lordfarq/openflight/src/openflight/rolling_buffer/monitor.py

"""
Rolling Buffer Monitor - Alternative to LaunchMonitor for rolling buffer mode.

Provides the same interface as LaunchMonitor but uses rolling buffer capture
and post-processing for higher resolution speed data and spin detection.
"""

import logging
import statistics
import threading
import time
from datetime import datetime
from typing import Callable, List, Optional

from ..launch_monitor import ClubType, Shot, estimate_carry_distance
from ..ops243 import OPS243Radar, SpeedReading
from ..session_logger import get_session_logger
from .processor import RollingBufferProcessor
from .trigger import create_trigger
from .types import ProcessedCapture

logger = logging.getLogger("openflight.rolling_buffer.monitor")


def get_optimal_spin_for_ball_speed(ball_speed_mph: float, club: ClubType = ClubType.DRIVER) -> float:
    """
    Get optimal spin rate for a given ball speed.

    Based on TrackMan/PING research data:
    - Higher ball speeds require LESS spin for optimal carry
    - Lower ball speeds need MORE spin to maintain lift

    Reference data points (driver):
    - 120 mph ball speed → ~2900 rpm optimal
    - 140 mph ball speed → ~2700 rpm optimal
    - 160 mph ball speed → ~2550 rpm optimal (Tour average zone)
    - 180 mph ball speed → ~2050 rpm optimal

    Args:
        ball_speed_mph: Ball speed in mph
        club: Club type (affects optimal spin)

    Returns:
        Optimal spin rate in RPM
    """
    # Driver optimal spin (baseline) - interpolated from TrackMan/PING data
    # Table: (min_speed, base_rpm_at_upper_bound, rpm_per_mph_below_upper, upper_bound)
    _spin_table = [
        (180, 2050, 0, 999),
        (170, 2050, 25, 180),
        (160, 2300, 25, 170),
        (140, 2550, 7.5, 160),
        (120, 2700, 10, 140),
        (100, 2900, 10, 120),
    ]

    optimal = 3200  # Default for speeds below 100 mph
    for min_speed, base_rpm, rpm_per_mph, upper in _spin_table:
        if ball_speed_mph >= min_speed:
            optimal = base_rpm + (upper - ball_speed_mph) * rpm_per_mph
            break

    # Adjust for club type - irons need more spin
    club_spin_multipliers = {
        ClubType.DRIVER: 1.0,
        ClubType.WOOD_3: 1.15,
        ClubType.WOOD_5: 1.25,
        ClubType.WOOD_7: 1.32,
        ClubType.HYBRID_3: 1.45,
        ClubType.HYBRID_5: 1.55,
        ClubType.HYBRID_7: 1.65,
        ClubType.HYBRID_9: 1.75,
        ClubType.IRON_2: 1.5,
        ClubType.IRON_3: 1.6,
        ClubType.IRON_4: 1.8,
        ClubType.IRON_5: 2.0,
        ClubType.IRON_6: 2.2,
        ClubType.IRON_7: 2.5,
        ClubType.IRON_8: 2.8,
        ClubType.IRON_9: 3.2,
        ClubType.PW: 3.6,
        ClubType.GW: 4.1,
        ClubType.SW: 4.3,
        ClubType.LW: 4.6,
        ClubType.UNKNOWN: 1.0,
    }

    multiplier = club_spin_multipliers.get(club, 1.0)
    return optimal * multiplier


def estimate_carry_with_spin(
    ball_speed_mph: float,
    spin_rpm: float,
    club: ClubType = ClubType.DRIVER,
    club_speed_mph: Optional[float] = None,
) -> float:
    """
    Estimate carry distance using ball speed, spin rate, and optional club speed.

    Based on TrackMan/PING research data and physics:
    - Ball speed is primary factor (~85% of distance variance)
    - Spin rate affects trajectory via Magnus effect (lift)
    - Optimal spin varies inversely with ball speed
    - Smash factor validates contact quality

    Reference data points (driver, optimal conditions):
    - 120 mph ball speed → ~198 yards carry
    - 140 mph ball speed → ~231 yards carry
    - 160 mph ball speed → ~271 yards carry (Tour average: 167 mph → 275 yds)
    - 180 mph ball speed → ~310 yards carry

    Spin effects:
    - Too LOW: Ball "falls out of sky" - significant distance loss
    - Optimal: Maximum carry for given ball speed
    - Too HIGH: Ball "balloons" - moderate distance loss

    Args:
        ball_speed_mph: Ball speed in mph
        spin_rpm: Spin rate in RPM
        club: Club type for distance calculation
        club_speed_mph: Optional club head speed for smash factor validation

    Returns:
        Estimated carry distance in yards
    """
    # Get base carry from existing lookup table (TrackMan-derived)
    base_carry = estimate_carry_distance(ball_speed_mph, club)

    # Calculate optimal spin for this ball speed and club
    optimal_spin = get_optimal_spin_for_ball_speed(ball_speed_mph, club)

    # Calculate spin deviation
    spin_delta = spin_rpm - optimal_spin
    spin_delta_abs = abs(spin_delta)

    # Apply asymmetric spin adjustment
    # Low spin hurts MORE than high spin (ball falls out of sky vs balloons)
    if spin_delta < 0:
        # LOW SPIN: More severe penalty
        # Research shows ~1.2 yards lost per 100 rpm below optimal
        # Cap at 18% max penalty for extremely low spin
        penalty_per_100rpm = 0.012  # 1.2% per 100 rpm
        spin_factor = 1.0 - (spin_delta_abs / 100) * penalty_per_100rpm
        spin_factor = max(0.82, spin_factor)
    else:
        # HIGH SPIN: Less severe penalty (ball balloons but still carries)
        # Research shows ~0.8 yards lost per 100 rpm above optimal
        # Cap at 12% max penalty for extremely high spin
        penalty_per_100rpm = 0.008  # 0.8% per 100 rpm
        spin_factor = 1.0 - (spin_delta_abs / 100) * penalty_per_100rpm
        spin_factor = max(0.88, spin_factor)

    # Slight bonus for being very close to optimal (within 200 rpm)
    if spin_delta_abs < 200:
        spin_factor = min(1.02, spin_factor + 0.01)

    # Smash factor quality adjustment (if club speed available)
    smash_factor_adj = 1.0
    if club_speed_mph and club_speed_mph > 0:
        smash = ball_speed_mph / club_speed_mph

        # Optimal smash factors by club type
        optimal_smash = {
            ClubType.DRIVER: 1.48,
            ClubType.WOOD_3: 1.44,
            ClubType.WOOD_5: 1.42,
            ClubType.WOOD_7: 1.41,
            ClubType.HYBRID_3: 1.39,
            ClubType.HYBRID_5: 1.37,
            ClubType.HYBRID_7: 1.35,
            ClubType.HYBRID_9: 1.33,
            ClubType.IRON_2: 1.36,
            ClubType.IRON_3: 1.35,
            ClubType.IRON_4: 1.33,
            ClubType.IRON_5: 1.31,
            ClubType.IRON_6: 1.29,
            ClubType.IRON_7: 1.27,
            ClubType.IRON_8: 1.25,
            ClubType.IRON_9: 1.23,
            ClubType.PW: 1.21,
            ClubType.GW: 1.19,
            ClubType.SW: 1.18,
            ClubType.LW: 1.17,
            ClubType.UNKNOWN: 1.35,
        }

        target_smash = optimal_smash.get(club, 1.35)
        smash_delta = target_smash - smash

        if smash_delta > 0:
            # Below optimal smash = off-center hit = less efficient energy transfer
            # Penalize ~3% per 0.05 smash factor below optimal
            smash_factor_adj = max(0.94, 1.0 - (smash_delta / 0.05) * 0.03)
        elif smash_delta < -0.05:
            # Unusually high smash factor (>1.53 for driver) - might be measurement error
            # Or could indicate gear effect adding speed - slight penalty for uncertainty
            smash_factor_adj = 0.98

    # Final calculation
    adjusted_carry = base_carry * spin_factor * smash_factor_adj

    return adjusted_carry


class RollingBufferMonitor:
    """
    Golf Launch Monitor using rolling buffer mode.

    Alternative to LaunchMonitor that captures raw I/Q data for post-processing.
    Provides higher temporal resolution (~937 Hz vs ~56 Hz) and optional spin
    detection.

    Recommended configuration uses "speed" trigger (default):
    - Fast speed detection mode (~150-200Hz) watches for club swing
    - Automatically switches to rolling buffer when speed detected
    - Captures ball impact with high temporal resolution
    - Per OmniPreSense manufacturer recommendation

    Interface matches LaunchMonitor for compatibility with existing code.

    Example:
        monitor = RollingBufferMonitor()  # Uses speed trigger by default
        monitor.connect()
        monitor.start(shot_callback=on_shot)

        # Wait for shots...

        monitor.stop()
        monitor.disconnect()
    """

    def __init__(
        self,
        port: Optional[str] = None,
        trigger_type: str = "speed",
        sample_rate_ksps: int = 30,
        **trigger_kwargs,
    ):
        """
        Initialize rolling buffer monitor.

        Args:
            port: Serial port for radar. Auto-detect if None.
            trigger_type: Trigger strategy:
                - "speed" (default, recommended): Fast speed trigger per manufacturer
                - "polling": Continuous capture polling (slower, simpler)
                - "threshold": Speed threshold trigger
                - "manual": External trigger for testing
            **trigger_kwargs: Arguments for trigger strategy
        """
        self.radar = OPS243Radar(port=port)
        self.processor = RollingBufferProcessor(sample_rate=sample_rate_ksps * 1000)
        self.trigger_type = trigger_type
        self.sample_rate_ksps = sample_rate_ksps
        self.trigger = create_trigger(trigger_type, **trigger_kwargs)

        self._running = False
        self._capture_thread: Optional[threading.Thread] = None
        self._shot_callback: Optional[Callable[[Shot], None]] = None
        self._live_callback: Optional[Callable[[SpeedReading], None]] = None
        self._shots: List[Shot] = []
        self._current_club: ClubType = ClubType.DRIVER

    def connect(self) -> bool:
        """
        Connect to radar and configure based on trigger type.

        For "speed" trigger: Configuration is handled by the trigger strategy
        For other triggers: Configure for rolling buffer mode with appropriate
        pre_trigger_segments from the trigger.

        Returns:
            True if successful
        """
        self.radar.connect()

        # Speed trigger handles its own configuration (starts in speed mode)
        # Other triggers need rolling buffer mode configured upfront
        if self.trigger_type != "speed":
            # Get pre_trigger_segments from the trigger if available
            pre_trigger_segments = getattr(self.trigger, 'pre_trigger_segments', 12)
            self.radar.configure_for_rolling_buffer(
                pre_trigger_segments=pre_trigger_segments,
                sample_rate_ksps=self.sample_rate_ksps,
            )
            logger.info("Rolling buffer mode configured with S#%d, S=%d", pre_trigger_segments, self.sample_rate_ksps)
        else:
            logger.info("Using speed trigger - configuration deferred to trigger")

        return True

    def disconnect(self):
        """Disconnect from radar."""
        self.stop()
        self.radar.disable_rolling_buffer()
        self.radar.disconnect()

    def get_radar_info(self) -> dict:
        """Get radar module information."""
        return self.radar.get_info()

    def start(
        self,
        shot_callback: Optional[Callable[[Shot], None]] = None,
        live_callback: Optional[Callable[[SpeedReading], None]] = None,
        diagnostic_callback: Optional[Callable[[dict], None]] = None,
    ):
        """
        Start monitoring for shots.

        Args:
            shot_callback: Called when a complete shot is detected
            live_callback: Called for live readings (limited in rolling buffer mode)
            diagnostic_callback: Called with trigger diagnostic data for UI display
        """
        self._shot_callback = shot_callback
        self._live_callback = live_callback
        self._diagnostic_callback = diagnostic_callback
        self._running = True

        self._capture_thread = threading.Thread(
            target=self._capture_loop,
            daemon=True,
        )
        self._capture_thread.start()

        logger.info("Rolling buffer monitor started (trigger: %s)", self.trigger_type)

    def stop(self):
        """Stop monitoring."""
        self._running = False
        if self._capture_thread:
            self._capture_thread.join(timeout=5.0)
            self._capture_thread = None
        logger.info("Rolling buffer monitor stopped")

    def _emit_diagnostics(self, wall_clock_ms: float = 0):
        """Drain trigger diagnostics and emit them to logger and UI."""
        diagnostics = self.trigger.drain_diagnostics()
        session_logger = get_session_logger()

        for diag in diagnostics:
            diag["trigger_type"] = self.trigger_type
            # Use trigger's own edge-to-S! latency if measured,
            # otherwise fall back to wall-clock (includes idle wait + serial transfer)
            latency = diag.pop("trigger_latency_ms", None) or wall_clock_ms
            diag["latency_ms"] = latency

            # Log to session JSONL
            if session_logger:
                session_logger.log_trigger_diagnostic(
                    trigger_type=self.trigger_type,
                    accepted=diag["accepted"],
                    reason=diag.get("reason", ""),
                    response_bytes=diag.get("response_bytes", 0),
                    total_readings=diag.get("total_readings", 0),
                    outbound_readings=diag.get("outbound_readings", 0),
                    inbound_readings=diag.get("inbound_readings", 0),
                    peak_outbound_mph=diag.get("peak_outbound_mph", 0),
                    peak_inbound_mph=diag.get("peak_inbound_mph", 0),
                    all_outbound_speeds=diag.get("all_outbound_speeds"),
                    all_inbound_speeds=diag.get("all_inbound_speeds"),
                    latency_ms=latency,
                )

            # Emit to UI via WebSocket
            if self._diagnostic_callback:
                self._diagnostic_callback(diag)

    def _capture_loop(self):
        """Main capture loop - wait for trigger, process, emit shot."""
        while self._running:
            try:
                trigger_start = time.time()

                # Wait for trigger and capture
                # Use a long timeout so sound/hardware triggers can wait
                # for the next swing without noisy timeout-restart cycles.
                capture = self.trigger.wait_for_trigger(
                    radar=self.radar,
                    processor=self.processor,
                    timeout=30.0,
                )

                trigger_latency_ms = (time.time() - trigger_start) * 1000

                # Always drain trigger diagnostics (captures in-loop rejections)
                self._emit_diagnostics(trigger_latency_ms)

                if capture is None:
                    continue

                # Process capture (FFT + speed/spin extraction)
                process_start = time.time()
                processed = self.processor.process_capture(capture)
                process_ms = (time.time() - process_start) * 1000
                logger.info("[PERF] process_capture: %.1fms", process_ms)

                if processed is None:
                    logger.warning("Failed to process capture")
                    # Emit diagnostic for processing failure
                    diag = {
                        "timestamp": capture.trigger_time if capture else 0,
                        "accepted": False,
                        "reason": "processing_failed",
                        "trigger_type": self.trigger_type,
                        "latency_ms": trigger_latency_ms,
                        "response_bytes": 0,
                        "total_readings": 0,
                        "outbound_readings": 0,
                        "inbound_readings": 0,
                        "peak_outbound_mph": 0,
                        "peak_inbound_mph": 0,
                        "all_outbound_speeds": [],
                        "all_inbound_speeds": [],
                    }
                    session_logger = get_session_logger()
                    if session_logger:
                        session_logger.log_trigger_diagnostic(
                            trigger_type=self.trigger_type,
                            accepted=False,
                            reason="processing_failed",
                            latency_ms=trigger_latency_ms,
                        )
                    if self._diagnostic_callback:
                        self._diagnostic_callback(diag)
                    continue

                # For speed trigger, use the trigger speed as club speed if not found in capture
                if (self.trigger_type == "speed" and
                    processed.club_speed_mph is None and
                    hasattr(self.trigger, 'last_trigger_speed')):
                    trigger_speed = self.trigger.last_trigger_speed
                    if trigger_speed > 0:
                        processed.club_speed_mph = trigger_speed
                        logger.info(f"Using trigger speed as club speed: {trigger_speed:.1f} mph")

                logger.debug(f"Processed: ball={processed.ball_speed_mph:.1f} mph, "
                            f"club={processed.club_speed_mph}")

                # Create shot
                shot = self._create_shot(processed)

                if shot:
                    self._shots.append(shot)
                    logger.info(
                        "Shot detected: ball=%.1f mph, club=%s, spin=%s",
                        shot.ball_speed_mph,
                        f"{shot.club_speed_mph:.1f}" if shot.club_speed_mph else "N/A",
                        f"{shot.spin_rpm:.0f}" if shot.spin_rpm else "N/A"
                    )

                    # Log raw I/Q data and trigger events to session logger
                    session_logger = get_session_logger()
                    if session_logger:
                        shot_number = len(self._shots)

                        # Log raw I/Q data for offline analysis
                        session_logger.log_rolling_buffer_capture(
                            shot_number=shot_number,
                            sample_time=capture.sample_time,
                            trigger_time=capture.trigger_time,
                            i_samples=capture.i_samples,
                            q_samples=capture.q_samples,
                            ball_speed_mph=shot.ball_speed_mph,
                            club_speed_mph=shot.club_speed_mph,
                            ball_timestamp_ms=processed.ball_timestamp_ms,
                            club_timestamp_ms=processed.club_timestamp_ms,
                            trigger_latency_ms=trigger_latency_ms,
                            smash_factor=processed.smash_factor,
                            spin_rpm=processed.spin.spin_rpm if processed.spin else None,
                            spin_confidence=processed.spin.confidence if processed.spin else None,
                            spin_quality=processed.spin.quality if processed.spin else None,
                            spin_snr=processed.spin.snr if processed.spin else None,
                        )

                        # Log accepted trigger event
                        session_logger.log_trigger_event(
                            trigger_type=self.trigger_type,
                            accepted=True,
                            peak_speed_mph=shot.ball_speed_mph,
                            readings_count=len(processed.timeline.readings),
                            latency_ms=trigger_latency_ms,
                        )

                        # Log detailed trigger diagnostic
                        all_outbound = [r for r in processed.timeline.readings if r.is_outbound]
                        all_inbound = [r for r in processed.timeline.readings if not r.is_outbound]
                        session_logger.log_trigger_diagnostic(
                            trigger_type=self.trigger_type,
                            accepted=True,
                            reason="accepted",
                            total_readings=len(processed.timeline.readings),
                            outbound_readings=len(all_outbound),
                            inbound_readings=len(all_inbound),
                            peak_outbound_mph=max((r.speed_mph for r in all_outbound), default=0),
                            peak_inbound_mph=max((r.speed_mph for r in all_inbound), default=0),
                            all_outbound_speeds=[r.speed_mph for r in all_outbound],
                            all_inbound_speeds=[r.speed_mph for r in all_inbound],
                            latency_ms=trigger_latency_ms,
                            ball_speed_mph=shot.ball_speed_mph,
                            club_speed_mph=shot.club_speed_mph,
                            spin_rpm=shot.spin_rpm,
                            carry_yards=shot.estimated_carry_yards,
                        )

                    # Emit diagnostic to UI
                    if self._diagnostic_callback:
                        self._diagnostic_callback({
                            "timestamp": datetime.now().isoformat(),
                            "accepted": True,
                            "reason": "accepted",
                            "trigger_type": self.trigger_type,
                            "latency_ms": trigger_latency_ms,
                            "response_bytes": 0,
                            "total_readings": len(processed.timeline.readings),
                            "outbound_readings": 0,
                            "inbound_readings": 0,
                            "peak_outbound_mph": shot.ball_speed_mph,
                            "peak_inbound_mph": 0,
                            "all_outbound_speeds": [],
                            "all_inbound_speeds": [],
                            "ball_speed_mph": shot.ball_speed_mph,
                            "club_speed_mph": shot.club_speed_mph,
                            "spin_rpm": shot.spin_rpm,
                            "carry_yards": shot.estimated_carry_yards,
                        })

                    if self._shot_callback:
                        callback_start = time.time()
                        self._shot_callback(shot)
                        callback_ms = (time.time() - callback_start) * 1000
                        total_ms = (time.time() - trigger_start) * 1000
                        logger.info(
                            "[PERF] shot_callback: %.1fms | total trigger-to-emit: %.1fms "
                            "(trigger: %.1fms, process: %.1fms, callback: %.1fms)",
                            callback_ms, total_ms,
                            trigger_latency_ms, process_ms, callback_ms,
                        )
                else:
                    logger.info(
                        "Shot validation failed: ball=%.1f mph (min 15 mph)",
                        processed.ball_speed_mph if processed else 0
                    )
                    # Emit diagnostic for shot validation failure
                    diag = {
                        "timestamp": datetime.now().isoformat(),
                        "accepted": False,
                        "reason": "shot_validation_failed",
                        "trigger_type": self.trigger_type,
                        "latency_ms": trigger_latency_ms,
                        "response_bytes": 0,
                        "total_readings": len(processed.timeline.readings) if processed else 0,
                        "outbound_readings": 0,
                        "inbound_readings": 0,
                        "peak_outbound_mph": processed.ball_speed_mph if processed else 0,
                        "peak_inbound_mph": 0,
                        "all_outbound_speeds": [],
                        "all_inbound_speeds": [],
                        "ball_speed_mph": processed.ball_speed_mph if processed else None,
                    }
                    session_logger = get_session_logger()
                    if session_logger:
                        session_logger.log_trigger_diagnostic(
                            trigger_type=self.trigger_type,
                            accepted=False,
                            reason="shot_validation_failed",
                            peak_outbound_mph=processed.ball_speed_mph if processed else 0,
                            total_readings=len(processed.timeline.readings) if processed else 0,
                            latency_ms=trigger_latency_ms,
                            ball_speed_mph=processed.ball_speed_mph if processed else None,
                        )
                    if self._diagnostic_callback:
                        self._diagnostic_callback(diag)

                # Reset trigger for next capture
                self.trigger.reset()

            except Exception as e:
                logger.error(f"Capture loop error: {e}")
                time.sleep(1.0)

    def _create_shot(self, processed: ProcessedCapture) -> Optional[Shot]:
        """
        Create Shot object from processed capture.

        Args:
            processed: Fully processed capture data

        Returns:
            Shot object or None if invalid
        """
        # Validate ball speed
        if processed.ball_speed_mph < 15:
            logger.debug(f"Ball speed too low: {processed.ball_speed_mph:.1f} mph")
            return None

        # Calculate carry distance
        # Use spin-adjusted carry only for reliable spin readings
        has_reliable_spin = processed.has_spin and processed.spin
        has_any_spin = processed.spin is not None and processed.spin.spin_rpm > 0

        if has_reliable_spin:
            carry = estimate_carry_with_spin(
                processed.ball_speed_mph,
                processed.spin.spin_rpm,
                self._current_club,
                club_speed_mph=processed.club_speed_mph,
            )
        else:
            carry = estimate_carry_distance(processed.ball_speed_mph, self._current_club)

        # Always pass spin data through if detected (even low quality)
        # The UI shows confidence indicators so the user can judge
        spin_rpm = processed.spin.spin_rpm if has_any_spin else None
        spin_confidence = processed.spin.confidence if has_any_spin else None

        # Create shot with extended fields
        shot = Shot(
            ball_speed_mph=processed.ball_speed_mph,
            timestamp=datetime.now(),
            club_speed_mph=processed.club_speed_mph,
            peak_magnitude=None,  # Not directly available in rolling buffer mode
            readings=[],  # Raw readings not stored (use ProcessedCapture instead)
            club=self._current_club,
            spin_rpm=spin_rpm,
            spin_confidence=spin_confidence,
            carry_spin_adjusted=carry if has_reliable_spin else None,
            mode="rolling-buffer",
        )

        return shot

    def wait_for_shot(self, timeout: float = 60) -> Optional[Shot]:
        """
        Wait for a shot to be detected.

        Args:
            timeout: Maximum seconds to wait

        Returns:
            Shot object or None if timeout
        """
        shot_detected: List[Shot] = []

        def on_shot(shot: Shot):
            shot_detected.append(shot)

        original_callback = self._shot_callback
        self._shot_callback = on_shot

        start = time.time()
        while not shot_detected and (time.time() - start) < timeout:
            time.sleep(0.1)

        self._shot_callback = original_callback

        return shot_detected[0] if shot_detected else None

    def get_session_stats(self) -> dict:
        """
        Get statistics for the current session.

        Returns:
            Dict with shot count, averages, etc.
        """
        if not self._shots:
            return {
                "shot_count": 0,
                "avg_ball_speed": 0,
                "max_ball_speed": 0,
                "min_ball_speed": 0,
                "avg_club_speed": None,
                "avg_smash_factor": None,
                "avg_carry_est": 0,
                "avg_spin_rpm": None,
                "mode": "rolling-buffer",
            }

        ball_speeds = [s.ball_speed_mph for s in self._shots]
        club_speeds = [s.club_speed_mph for s in self._shots if s.club_speed_mph]
        smash_factors = [s.smash_factor for s in self._shots if s.smash_factor]

        # Get spin data
        spin_rpms = [
            s.spin_rpm
            for s in self._shots
            if s.spin_rpm is not None
        ]

        return {
            "shot_count": len(self._shots),
            "avg_ball_speed": statistics.mean(ball_speeds),
            "max_ball_speed": max(ball_speeds),
            "min_ball_speed": min(ball_speeds),
            "std_dev": statistics.stdev(ball_speeds) if len(ball_speeds) > 1 else 0,
            "avg_club_speed": statistics.mean(club_speeds) if club_speeds else None,
            "avg_smash_factor": statistics.mean(smash_factors) if smash_factors else None,
            "avg_carry_est": statistics.mean([s.estimated_carry_yards for s in self._shots]),
            "avg_spin_rpm": statistics.mean(spin_rpms) if spin_rpms else None,
            "spin_detection_rate": len(spin_rpms) / len(self._shots) if self._shots else 0,
            "mode": "rolling-buffer",
        }

    def get_shots(self) -> List[Shot]:
        """Get all detected shots."""
        return self._shots.copy()

    def clear_session(self):
        """Clear all recorded shots."""
        self._shots = []

    def set_club(self, club: ClubType):
        """Set the current club for future shots."""
        self._current_club = club

    def __enter__(self):
        """Context manager entry."""
        self.connect()
        return self

    def __exit__(self, exc_type, exc_val, exc_tb):
        """Context manager exit."""
        self.disconnect()
        return False
